DhamuVkl/ESP32S3-AI-Voice-Assistant/docs/mcp-based-graph.jpg

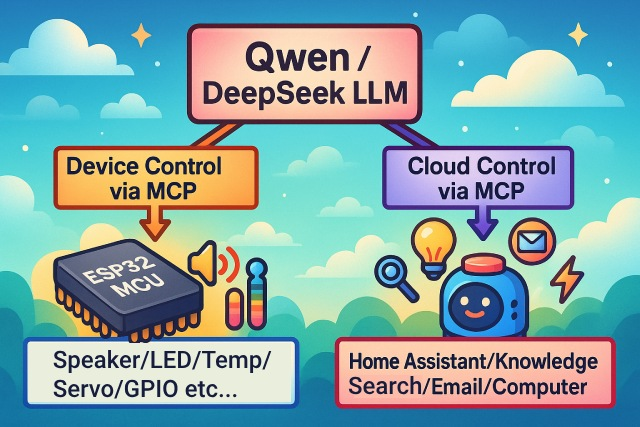
docs/mcp-based-graph.jpg
