DhamuVkl/ESP32S3-AI-Voice-Assistant/docs/v1/atoms3r.jpg

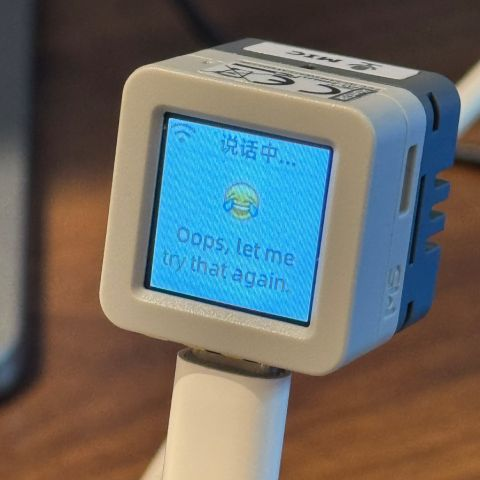
docs/v1/atoms3r.jpg
