DhamuVkl/ESP32S3-AI-Voice-Assistant/docs/v1/electron-bot.png

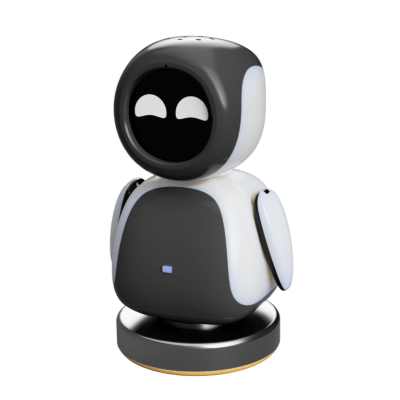
docs/v1/electron-bot.png
