DhamuVkl/ESP32S3-AI-Voice-Assistant/docs/v1/esp-hi.jpg

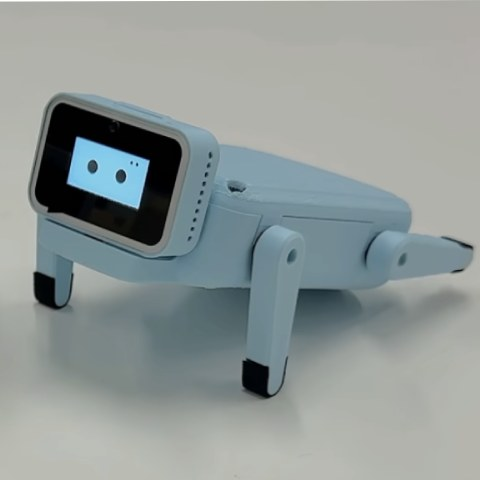
docs/v1/esp-hi.jpg
