DhamuVkl/ESP32S3-AI-Voice-Assistant/docs/v1/lichuang-s3.jpg

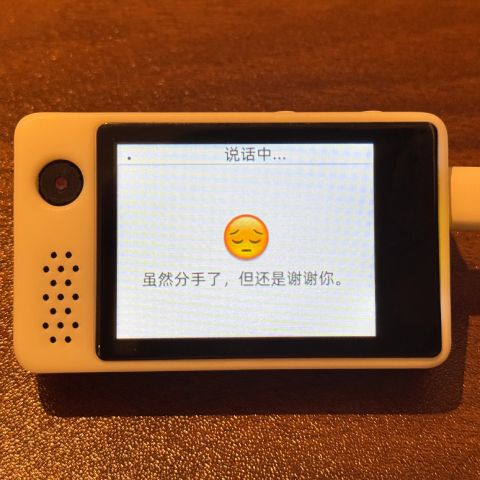
docs/v1/lichuang-s3.jpg
