DhamuVkl/ESP32S3-AI-Voice-Assistant/docs/v1/m5cores3.jpg

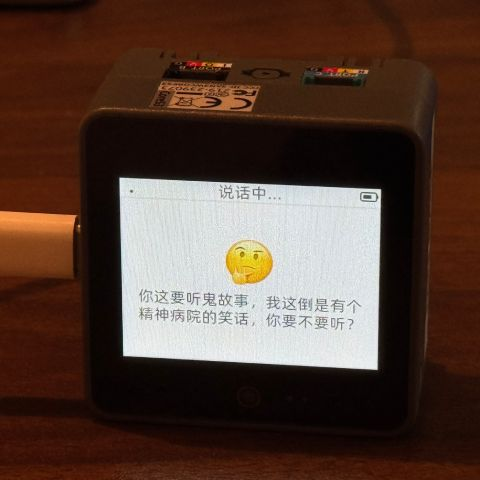
docs/v1/m5cores3.jpg
