DhamuVkl/ESP32S3-AI-Voice-Assistant/docs/v1/magiclick.jpg

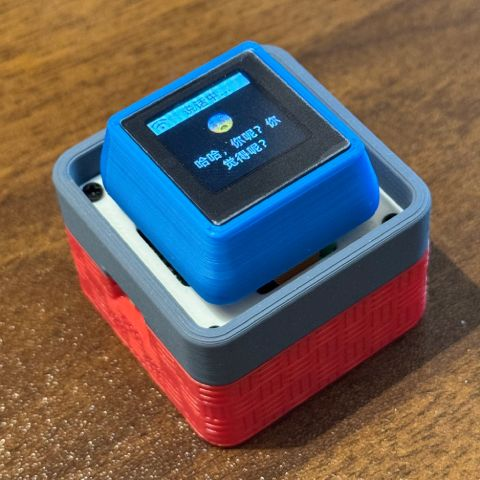
docs/v1/magiclick.jpg
