DhamuVkl/ESP32S3-AI-Voice-Assistant/docs/v1/otto-robot.png

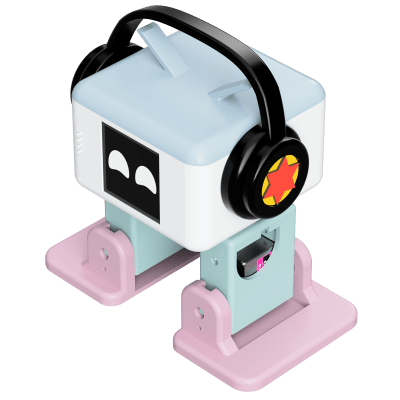
docs/v1/otto-robot.png
