DhamuVkl/ESP32S3-AI-Voice-Assistant/docs/v1/sensecap_watcher.jpg

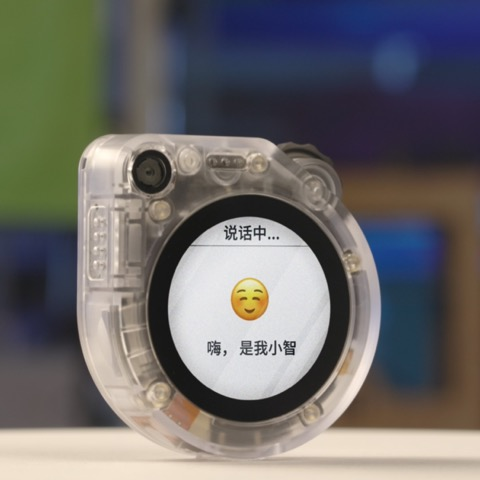
docs/v1/sensecap_watcher.jpg
