DhamuVkl/ESP32S3-AI-Voice-Assistant/docs/v1/xmini-c3.jpg

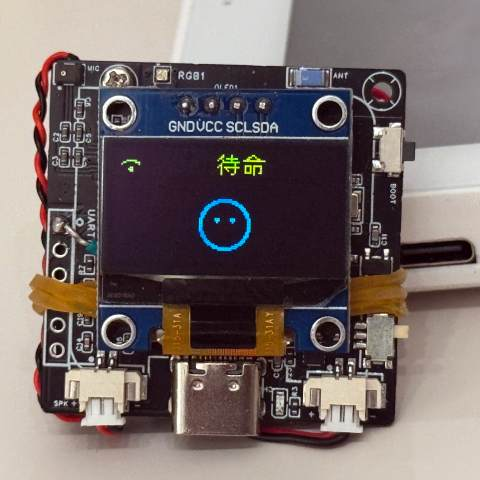
docs/v1/xmini-c3.jpg
