DhamuVkl/ESP32S3-AI-Voice-Assistant/scripts/p3_tools/img/img.png

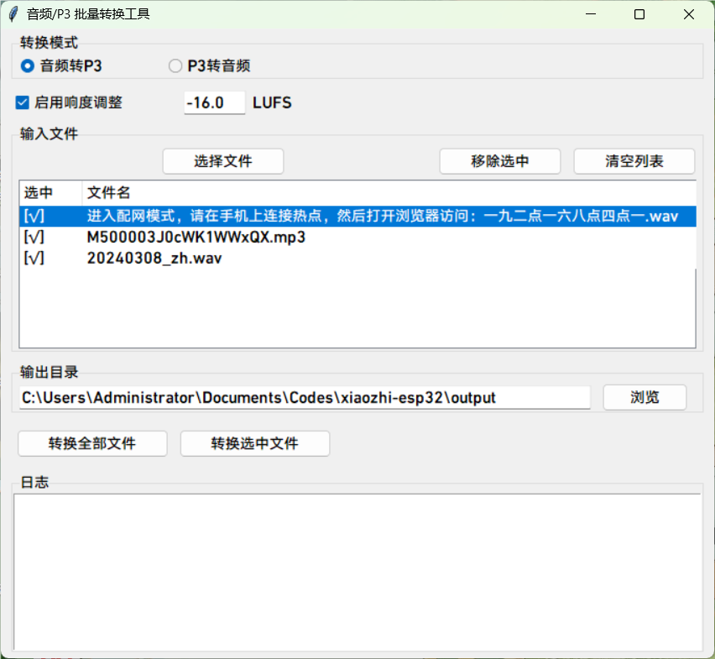
scripts/p3_tools/img/img.png
